lightningspore/seedsigner-luckfox-pico/test_suite/test_camera.py

import cv2

cap = cv2.VideoCapture('/dev/video0')

while cap.isOpened():
    ret, frame = cap.read()
    if ret:
        cv2.imshow('Frame', frame)
        if cv2.waitKey(1) & 0xFF == ord('q'):
            break

cap.release()

cv2.destroyAllWindows()
