lightningspore/seedsigner-luckfox-pico/test_suite/test_lcd.py

from hardware.ST7789 import ST7789

from PIL import Image
import random
from time import sleep

# Define the dimensions
width, height = 240, 240


def random_image():
    # Create a new image with RGB mode
    img = Image.new('RGB', (width, height))
    # Generate random colors for each pixel
    pixels = []
    for y in range(height):
        for x in range(width):
            pixels.append((random.randint(0, 255), random.randint(0, 255), random.randint(0, 255)))
    # Update the image with the generated colors
    img.putdata(pixels)
    return img


def solid_color_image(r,g,b):
    # Create a new image with RGB mode
    img = Image.new('RGB', (width, height))
    # Generate random colors for each pixel
    pixels = []
    for y in range(height):
        for x in range(width):
            pixels.append((r, g, b))
    # Update the image with the generated colors
    img.putdata(pixels)
    return img 

def test_loop():
    try:
        while True:
            rimg = random_image()
            disp.ShowImage(rimg, 0, 0)
            sleep(1)

            yellow_img = solid_color_image(255, 238, 109)
            disp.ShowImage(yellow_img, 0, 0)
            sleep(1)

            orange_img = solid_color_image(255, 100, 0)
            disp.ShowImage(orange_img, 0, 0)
            sleep(1)

            violet_img = solid_color_image(103, 78, 167)
            disp.ShowImage(violet_img, 0, 0)
            sleep(1)
    except KeyboardInterrupt:
        pass

# Intialize display library
disp = ST7789()

test_loop()

rimg = random_image()
disp.ShowImage(rimg, 0, 0)

yellow_img = solid_color_image(255,238,109)
disp.ShowImage(yellow_img, 0, 0)


orange_img = solid_color_image(255,100,0)
disp.ShowImage(orange_img, 0, 0)


violet_img = solid_color_image(103,78,167)
disp.ShowImage(violet_img, 0, 0)
